sanworks/PulsePal/Firmware/PulsePal3/Playback.ino

/*
----------------------------------------------------------------------------

This file is part of the Pulse Pal Project
Copyright (C) 2026 Sanworks LLC, Rochester, NY, USA

----------------------------------------------------------------------------

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
*/


// Pulse train playback. handler() is the hardware timer callback that plays pulse trains on all output
// channels (see the description above it). The other functions support it.
//
// Functions in this file:
//   TC3_Handler() (HW2 only)
//   mirrorAboutZero()
//   pulseFitsInBurst()
//   pulseFitsInTrain()
//   handler()
//   killChannel()
//   AbortAllPulseTrains()
//   updateUsesBursts()

#if (HARDWARE_VERSION == 2)
  // Interrupt service routine for timer counter TC3, configured in startHardwareTimer(). On Pulse Pal 3, IntervalTimer calls handler() directly.
  void TC3_Handler(void) {
    TC_GetStatus(TC1, 0); // Read the status register to clear the interrupt
    handler();
  }
#endif

// Returns the DAC code for the same voltage with the opposite sign. Used for phase 2 of biphasic custom pulses.
static inline uint16_t mirrorAboutZero(uint16_t dacCode) {
  if (dacCode < 32768) {
    uint32_t mirrored = 32768 + (32768 - (uint32_t)dacCode);
    if (mirrored > 65535) {
      return 65535; // -10V mirrors to +10V, the top of the DAC range
    }
    return (uint16_t)mirrored;
  } else {
    return 32768 - (dacCode - 32768);
  }
}

// True if a pulse starting on an output channel (0-3) now would end before its burst does. The end of a burst sets the
// resting voltage whatever phase is playing, so a biphasic pulse must fit whole: cut short, it loses part or all of
// phase 2 and is no longer charge balanced. A monophasic pulse needs only its phase 1 to fit.
static inline bool pulseFitsInBurst(byte channel) {
  uint32_t pulseEnd = SystemTime + Phase1Duration[channel];
  if (IsBiphasic[channel]) {
    pulseEnd += InterPhaseInterval[channel] + Phase2Duration[channel];
  }
  return pulseEnd < NextBurstTransitionTime[channel];
}
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
